Mysteriza/ESP8266Display-BME680/src/types.h

#ifndef TYPES_H
#define TYPES_H

enum AppMode
{
  MODE_OFFLINE,
  MODE_BME_ERROR,
  MODE_POWER_CRITICAL
};

enum OledDisplayState
{
  OLED_STATE_ERROR_SCREEN,
  OLED_STATE_DATA_SCREEN_1,
  OLED_STATE_DATA_SCREEN_2,
  OLED_STATE_DATA_SCREEN_3,
  OLED_STATE_DATA_SCREEN_4,
  OLED_STATE_OFF
};

enum ThermalState
{
  THERM_NORMAL,
  THERM_HOT_HOLD
};

enum PowerState
{
  POWER_ACTIVE,
  POWER_DISPLAY_OFF,
  POWER_SLEEP_PREP,
  POWER_CRITICAL
};

#endif
